Apfelholz/Dynamic-Project-Display-Module/aliExpress.png

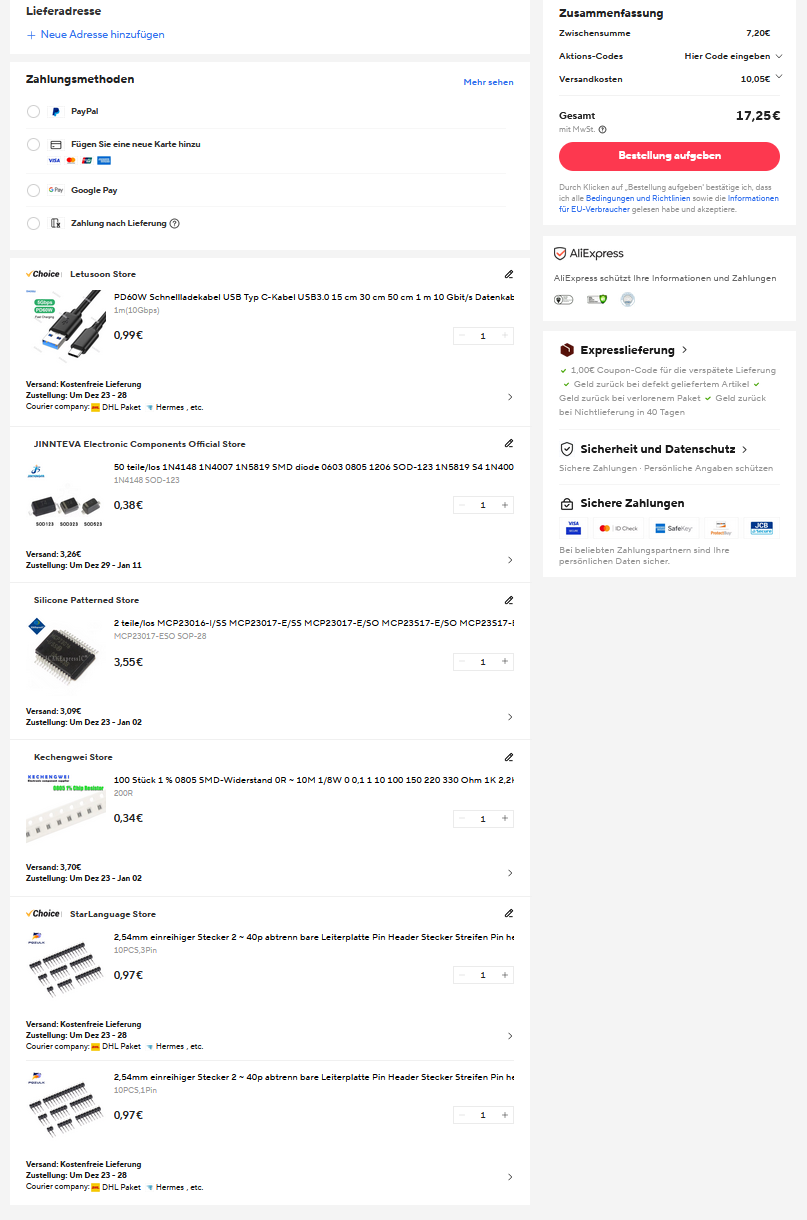
aliExpress.png
